uysan/iot-esp-eth/antenna/simulation/ff1.png

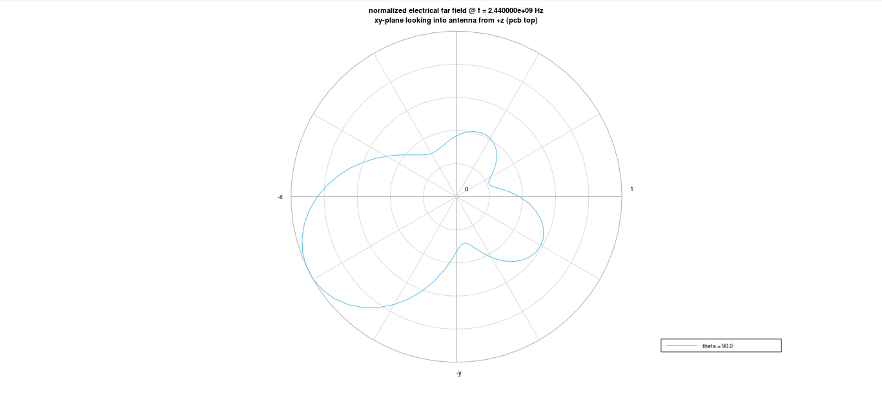
antenna/simulation/ff1.png
