uysan/iot-esp-eth/antenna/simulation/ff4.png

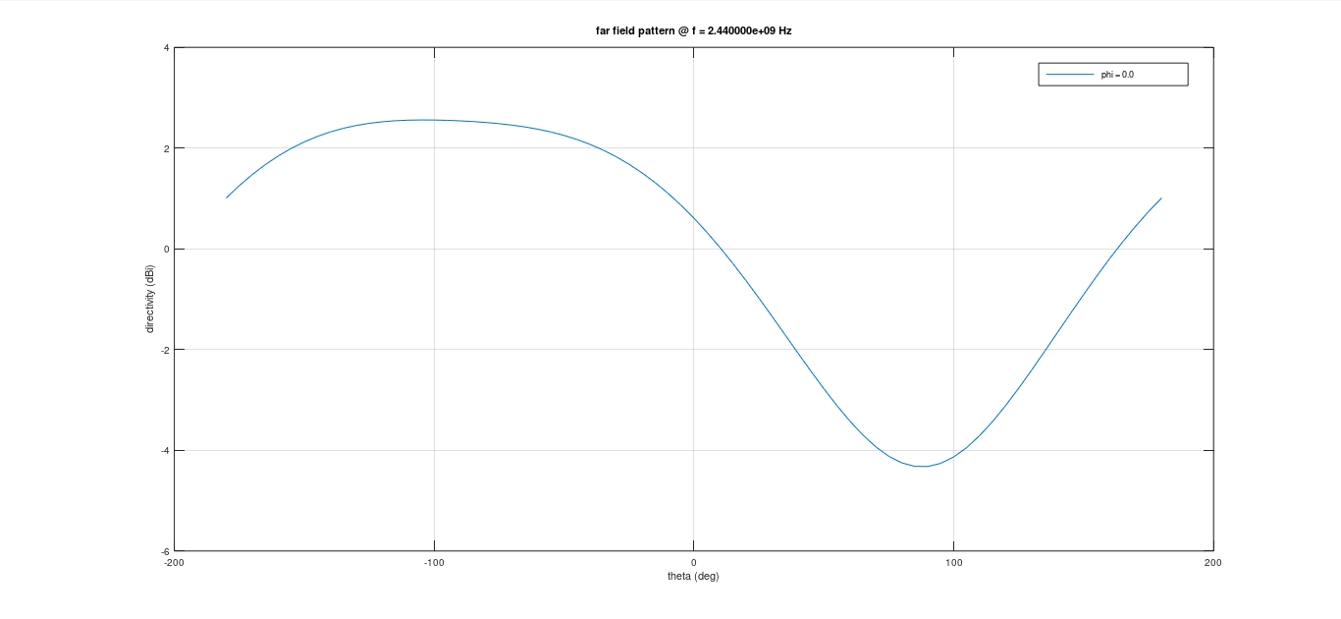
antenna/simulation/ff4.png
