uysan/iot-esp-eth/antenna/simulation/ff6.png

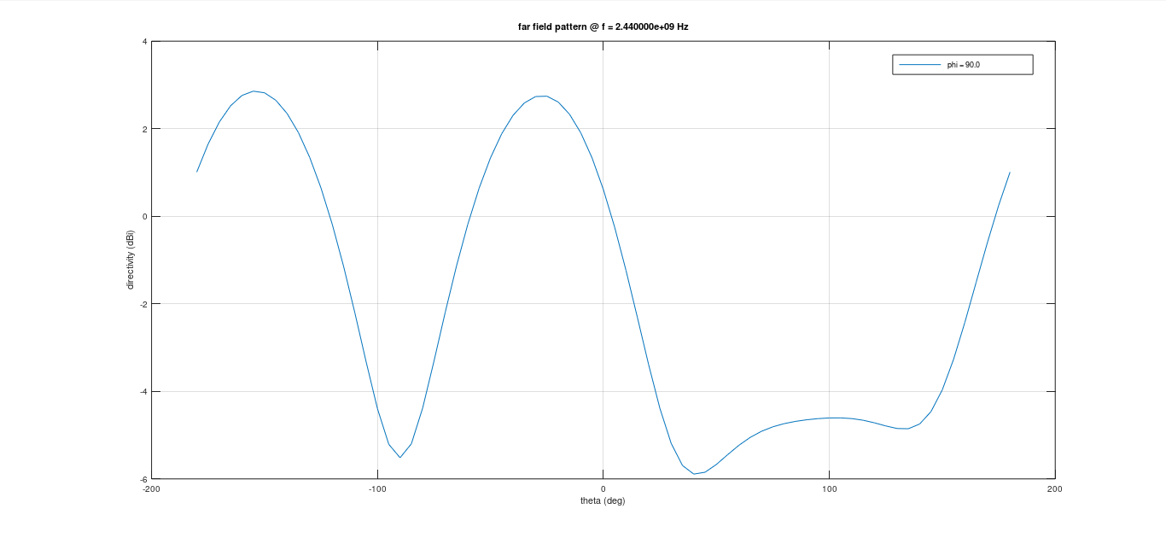
antenna/simulation/ff6.png
