uysan/iot-esp-eth/pcb/antviewb.png

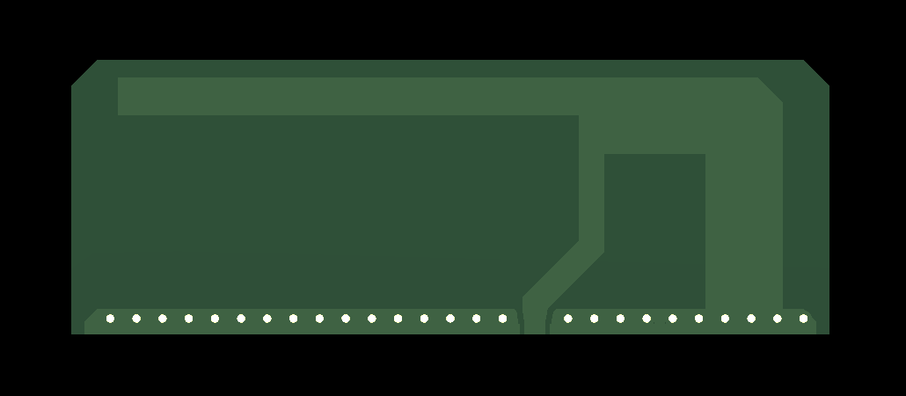
pcb/antviewb.png
